ruhiyusuf/photodetector/final_designs/Photodetector_v2_3_HI.asc

C1: cap; 0.22µ
C2: cap; 2.2µ
C3: cap; 104
C4: cap; 1µ
C5: cap; 0.1µ
C6: cap; 1µ
C7: cap; 226
C8: cap; 105
C10: cap; 226
C11: cap; 104
C12: cap; 104
C13: cap; 1p
C14: cap; 104
C15: cap; 104
C16: cap; 10n
C17: cap; 500p
I1: current; 0; AC 2m
R1: res; 1m
R2: res; 25k
R3: res; 220k
R4: res; 330
R5: res; 220
R6: res; 220
R7: res; 100
R8: res; 100
R9: res; 2.2
R10: res; 2.2
R11: res; 5k
R12: res; 2.2k
R13: res; 110k
R14: res; 2.2k
R15: res; 2.2
R16: res; 2.2
R17: res; 50
R18: res; 19.6
R19: res; 5k
R20: res; 19.6
R21: res; 19.6
R22: res; 19.6
R23: res; 19.6
R24: res; 19.6
U1: LMH6624
U3: LM7805
U4: DI_BZX84C3V3
U5: DI_BZX84C3V3
U6: LM7905
U9: OP27
V3: voltage; 20
V4: voltage; -20
Named nets: 0, AC, DC
CON3
.dc R1 0 5k 500
.ac dec 1000 1 60Meg
op27 gets regulated V-
Zener diode direction flipped
op27 gets regulated V+
step param R1 1k 10k 10k
.op
meas Vout AVG V(n020)
step param R19 9k 1m 1k
