ruhiyusuf/photodetector/Draft1.asc

R1: res
R2: res
R3: res
U1: OP27
Named nets: 0
